Leo-Pichelbauer/electrostatic-magic-wand/Scematic.kicad_sch

## KiCad design Scematic.kicad_sch (2024-08-11)

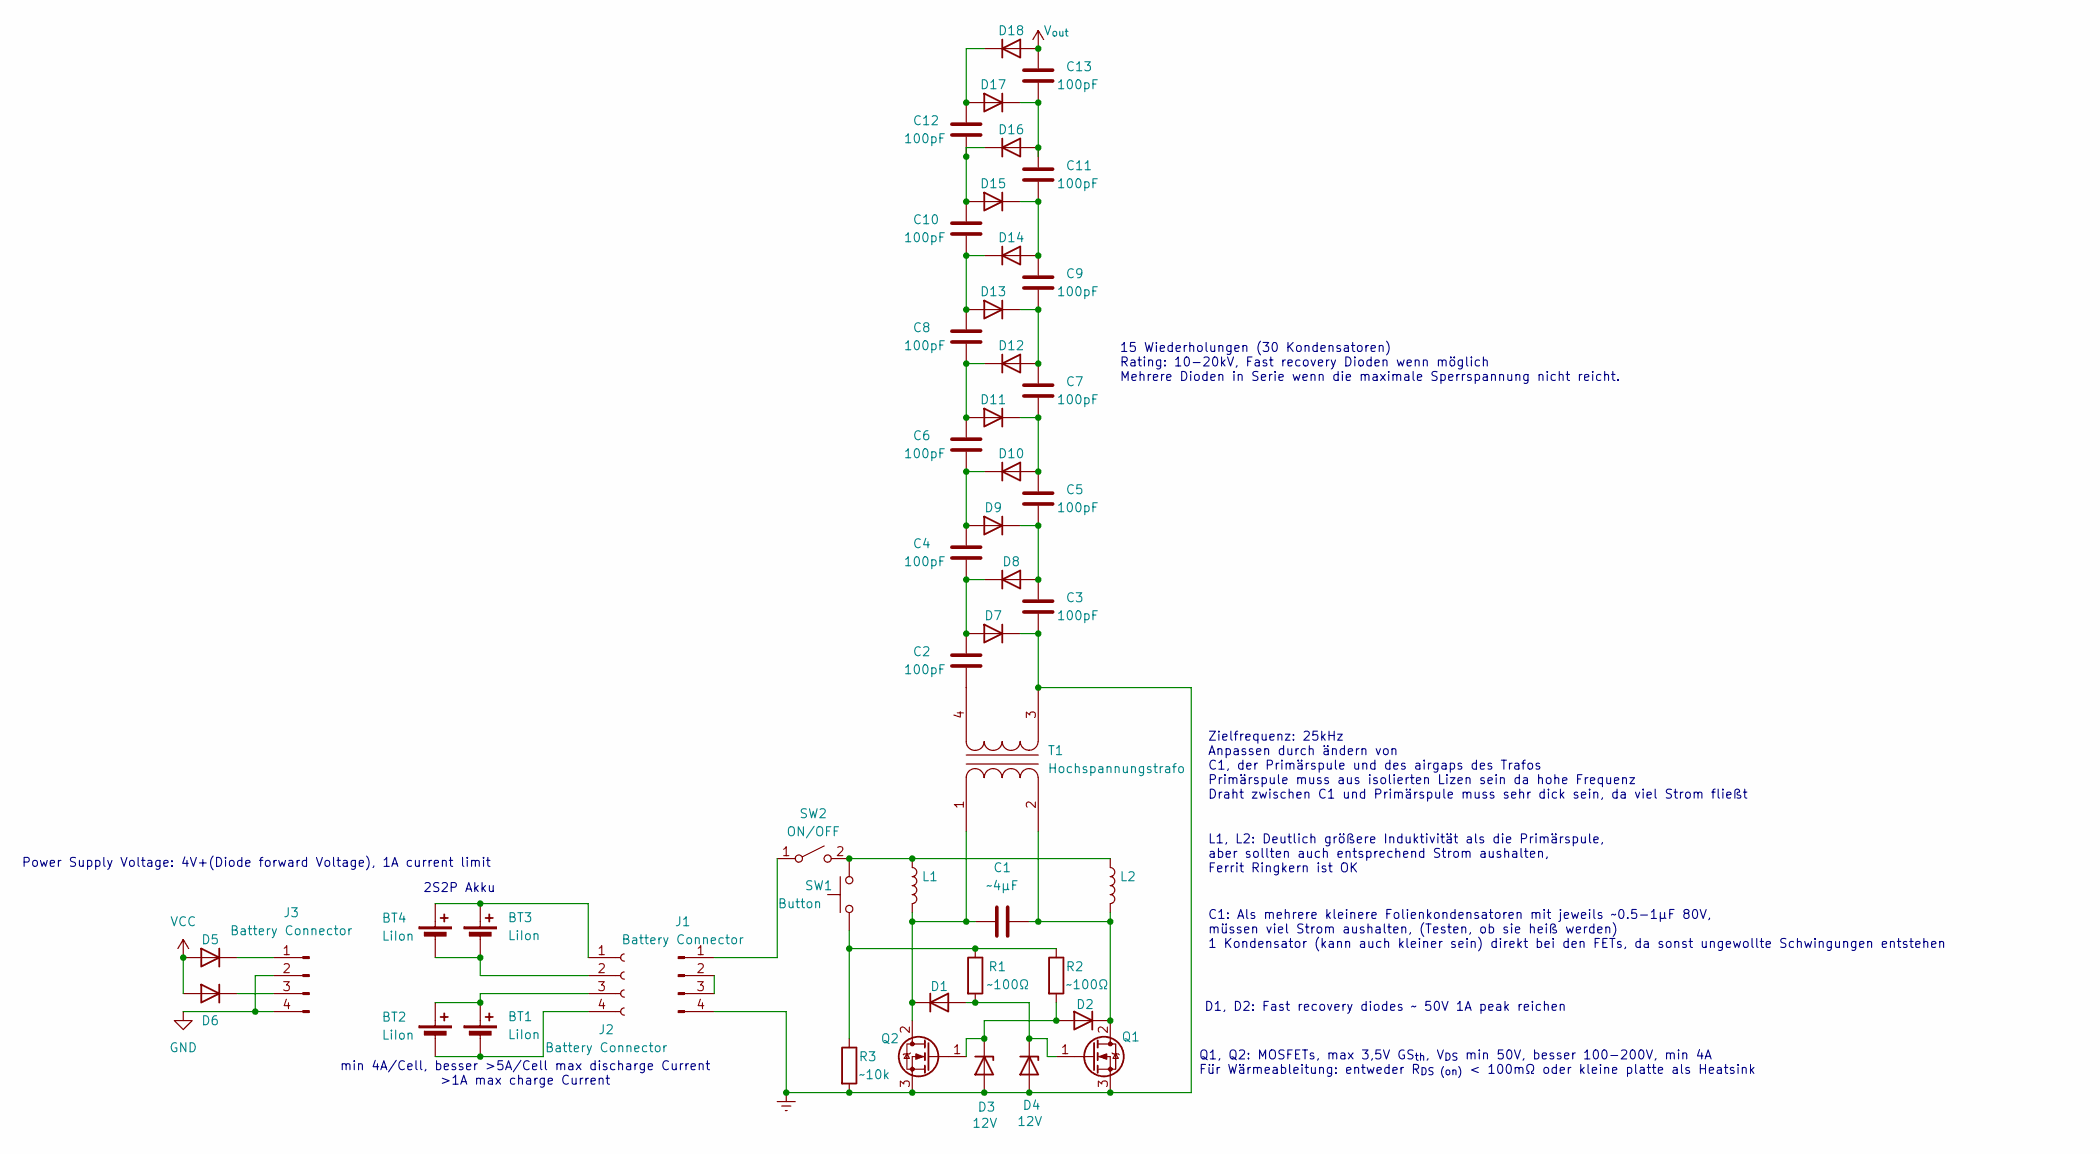
[picture p5: schematic Scematic.kicad_sch]

Parts:
BT1, BT2, BT3, BT4: LiIon
C1: ~4µF
C2, C3, C4, C5, C6, C7, C8, C9, C10, C11, C12, C13: 100pF
D1, D2, D5, D6, D7, D8, D9, D10, D11, D12, D13, D14, D15, D16, D17, D18: D
D3, D4: 12V
J1, J2, J3: Battery Connector
L1, L2: L
Q1, Q2: TO-220-3_Vertical
R1, R2: ~100Ω
R3: ~10k
SW1: Button
SW2: ON/OFF
T1: Hochspannungstrafo

Connections:
Earth: C3.2, D3.2 (A), D4.2 (A), D7.1 (K), J1.4, Q1.3 (S), Q2.3 (S), R3.2, T1.3 (SA)
GND: J3.2, J3.4
unnamed: BT1.1 (+), BT2.1 (+), J2.3
unnamed: BT1.2 (-), BT2.2 (-), J2.4
unnamed: BT3.1 (+), BT4.1 (+), J2.1
unnamed: BT3.2 (-), BT4.2 (-), J2.2
unnamed: C1.1, D1.1 (K), L1.2, Q2.2 (D), T1.1 (AA)
unnamed: C1.2, D2.1 (K), L2.2, Q1.2 (D), T1.2 (AB)
unnamed: C2.1, C4.2, D7.2 (A), D8.1 (K)
unnamed: C2.2, T1.4 (SB)
unnamed: C3.1, C5.2, D8.2 (A), D9.1 (K)
unnamed: C4.1, C6.2, D9.2 (A), D10.1 (K)
unnamed: C5.1, C7.2, D10.2 (A), D11.1 (K)
unnamed: C6.1, C8.2, D11.2 (A), D12.1 (K)
unnamed: C7.1, C9.2, D12.2 (A), D13.1 (K)
unnamed: C10.1, C12.2, D15.2 (A), D16.1 (K)
unnamed: C8.1, C10.2, D13.2 (A), D14.1 (K)
unnamed: C11.1, C13.2, D16.2 (A), D17.1 (K)
unnamed: C9.1, C11.2, D14.2 (A), D15.1 (K)
unnamed: C12.1, D17.2 (A), D18.1 (K)
unnamed: D1.2 (A), D4.1 (K), Q1.1 (G), R1.2
unnamed: D2.2 (A), D3.1 (K), Q2.1 (G), R2.2
unnamed: D5.1 (K), J3.1
unnamed: D6.1 (K), J3.3
unnamed: J1.1, SW2.1 (A)
unnamed: J1.2, J1.3
unnamed: L1.1, L2.1, SW1.2, SW2.2 (B)
unnamed: R1.1, R2.1, R3.1, SW1.1
VCC: D5.2 (A), D6.2 (A)
V_{out}: C13.1, D18.2 (A)

Notes on the sheet:
min 4A/Cell, besser >5A/Cell max discharge Current >1A max charge Current
Q1, Q2: MOSFETs, max 3,5V GS_{th}, V_{DS} min 50V, besser 100-200V, min 4A Für Wärmeableitung: entweder R_{DS (on)} < 100mΩ oder kleine platte als Heatsink
2S2P Akku
L1, L2: Deutlich größere Induktivität als die Primärspule, aber sollten auch entsprechend Strom aushalten, Ferrit Ringkern ist OK
Power Supply Voltage: 4V+(Diode forward Voltage), 1A current limit
C1: Als mehrere kleinere Folienkondensatoren mit jeweils ~0.5-1µF 80V, müssen viel Strom aushalten, (Testen, ob sie heiß werden) 1 Kondensator (kann auch kleiner sein) direkt bei den FETs, da sonst ungewollte Schwingungen entstehen
D1, D2: Fast recovery diodes ~ 50V 1A peak reichen
Zielfrequenz: 25kHz Anpassen durch ändern von C1, der Primärspule und des airgaps des Trafos Primärspule muss aus isolierten Lizen sein da hohe Frequenz Draht zwischen C1 und Primärspule muss sehr dick sein, da viel Strom fließt
15 Wiederholungen (30 Kondensatoren) Rating: 10-20kV, Fast recovery Dioden wenn möglich Mehrere Dioden in Serie wenn die maximale Sperrspannung nicht reicht.
